Prenda312/Track-base-robot-CAD/motor/motor.SLDPRT

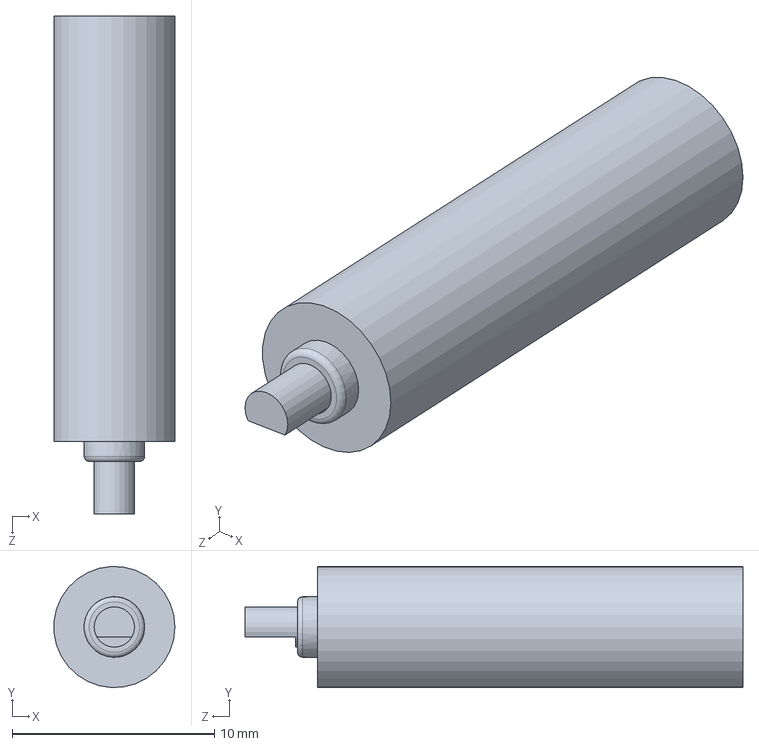
[picture p15: CAD file, 2024-11-09]
motor/motor.SLDPRT
5.98 x 5.99 x 24.6 mm
