Prenda312/Track-base-robot-CAD/worm/右旋蜗杆2×0.5-single.SLDPRT

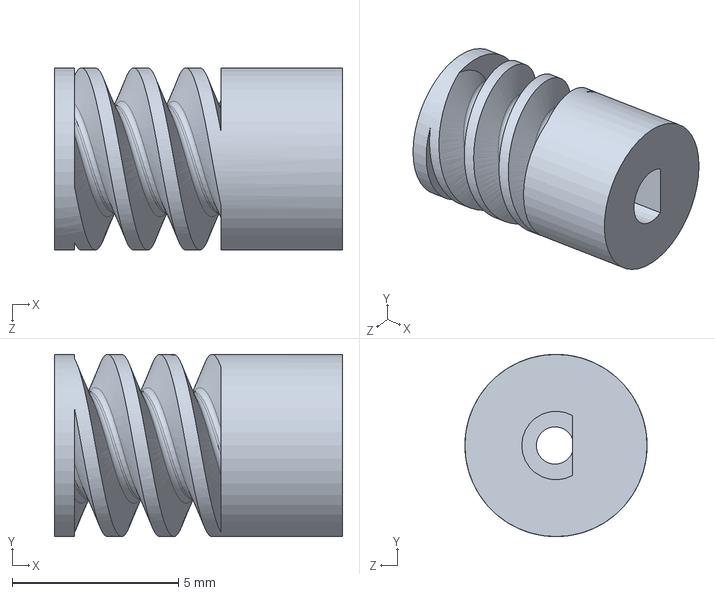
[picture p16: CAD file, 2024-11-09]
worm/右旋蜗杆2×0.5-single.SLDPRT
8.66 x 5.48 x 5.48 mm
