Prenda312/Track-base-robot-CAD/推力球轴承/推力球轴承_2.SLDPRT

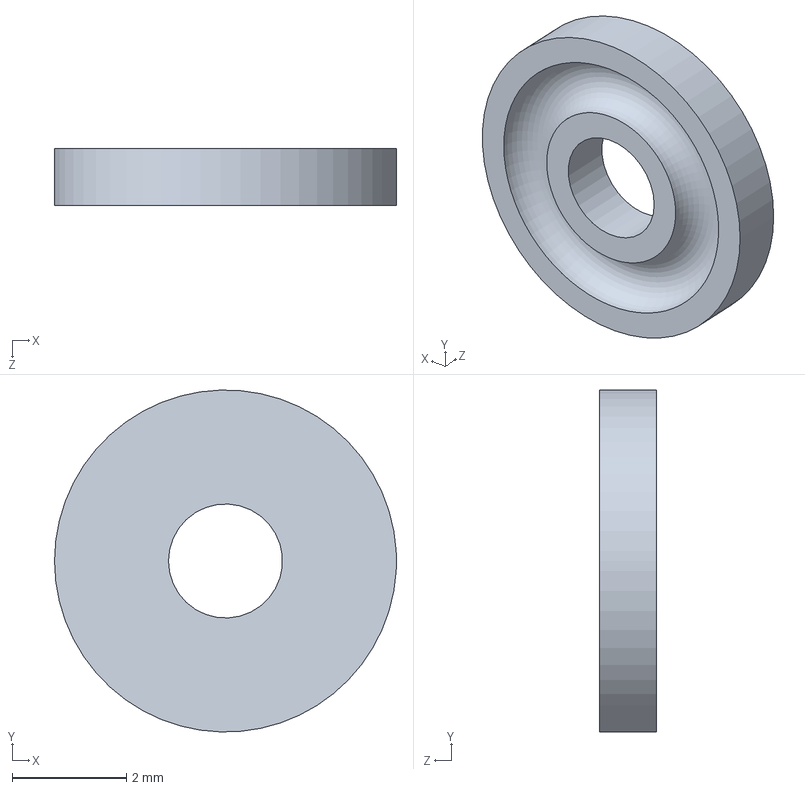
[picture p17: CAD file, 2024-11-09]
推力球轴承/推力球轴承_2.SLDPRT
6.00 x 6.00 x 1.00 mm
