Prenda312/Track-base-robot-CAD/轴/电机轴.SLDPRT

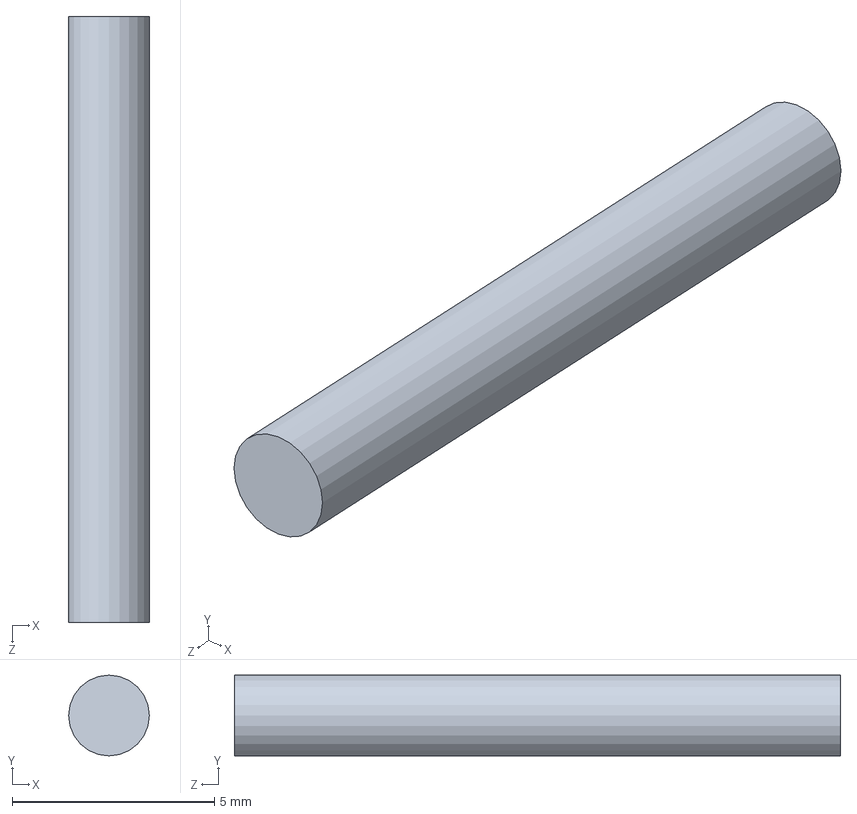
[picture p18: CAD file, 2024-11-09]
轴/电机轴.SLDPRT
2.00 x 2.00 x 15.0 mm
