Prenda312/Track-base-robot-CAD/motor/240-motor.SLDPRT

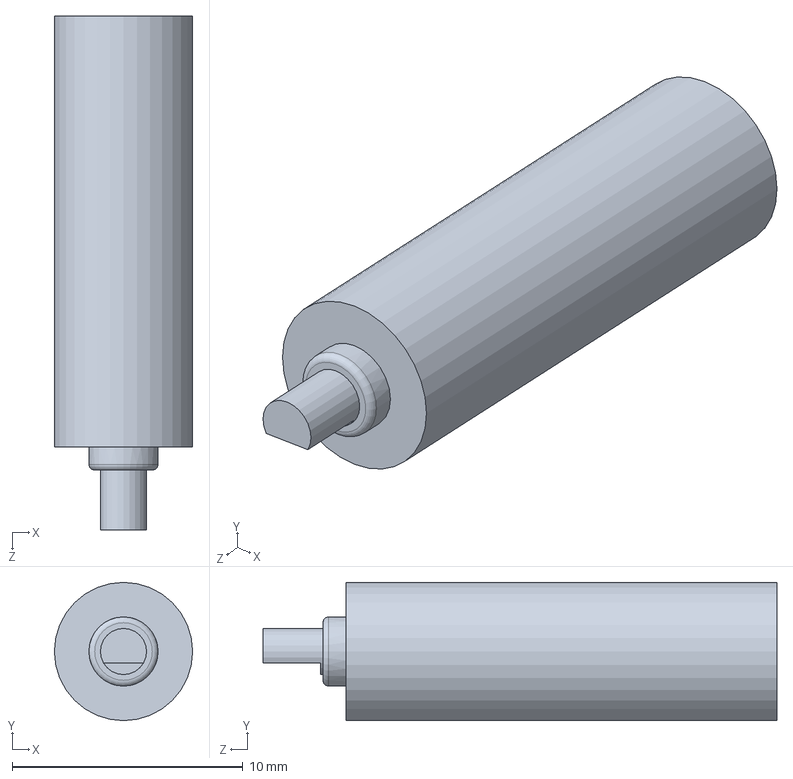
[picture p19: CAD file, 2024-11-09]
motor/240-motor.SLDPRT
6.00 x 6.00 x 22.3 mm
