Prenda312/Track-base-robot-CAD/spur gear-20×0.5.SLDPRT

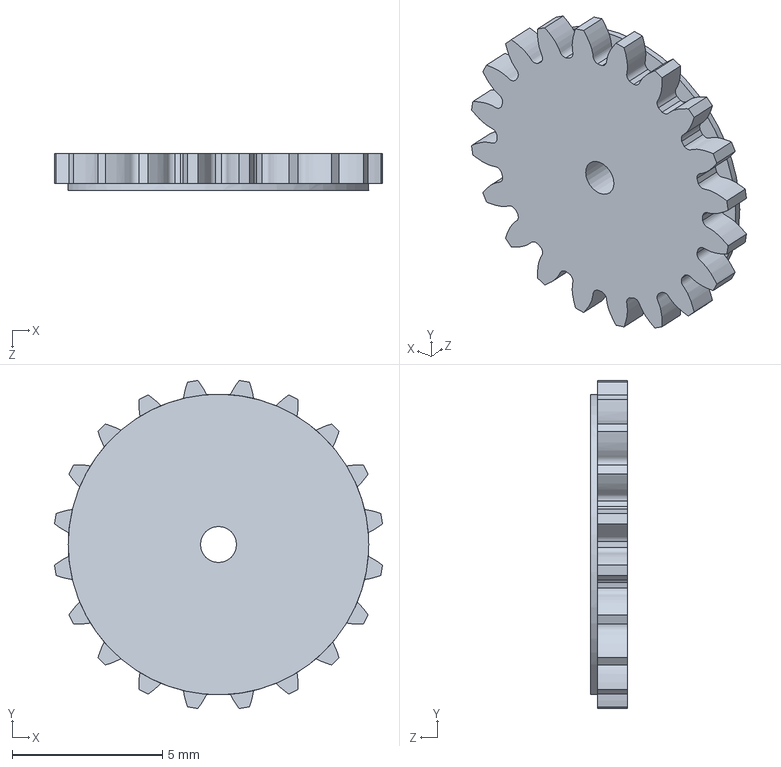
[picture p20: CAD file, 2024-11-09]
spur gear-20×0.5.SLDPRT
10.9 x 10.9 x 1.22 mm
