Prenda312/Track-base-robot-CAD/轴/8mm 轴.SLDPRT

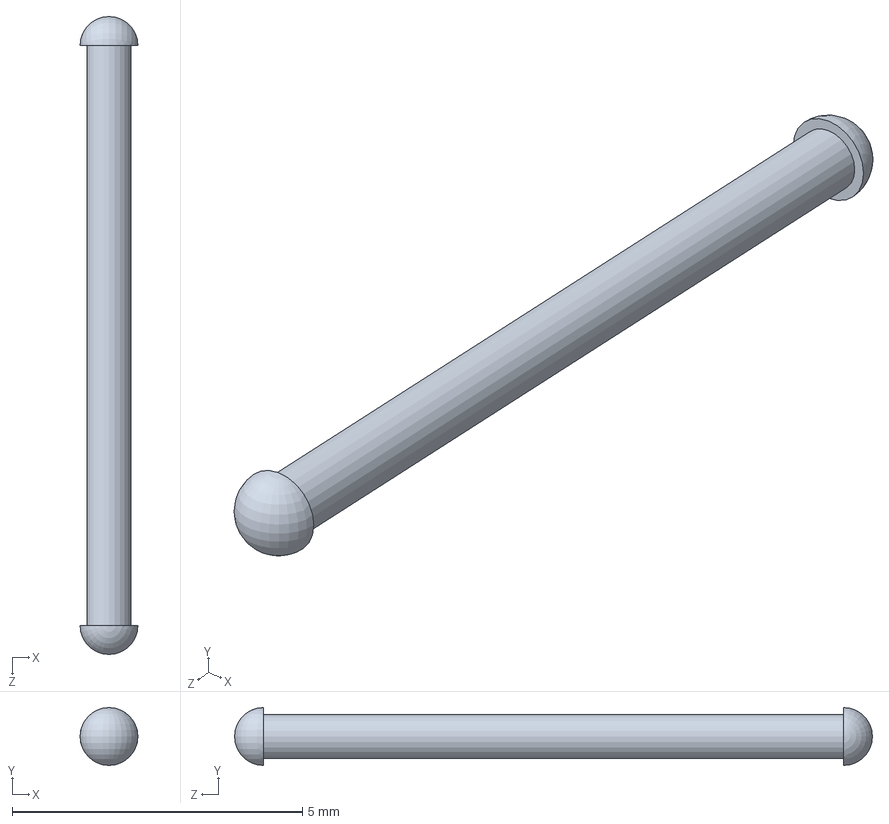
[picture p21: CAD file, 2024-11-09]
轴/8mm 轴.SLDPRT
1.00 x 1.00 x 11.0 mm
