Prenda312/Track-base-robot-CAD/camera.SLDPRT

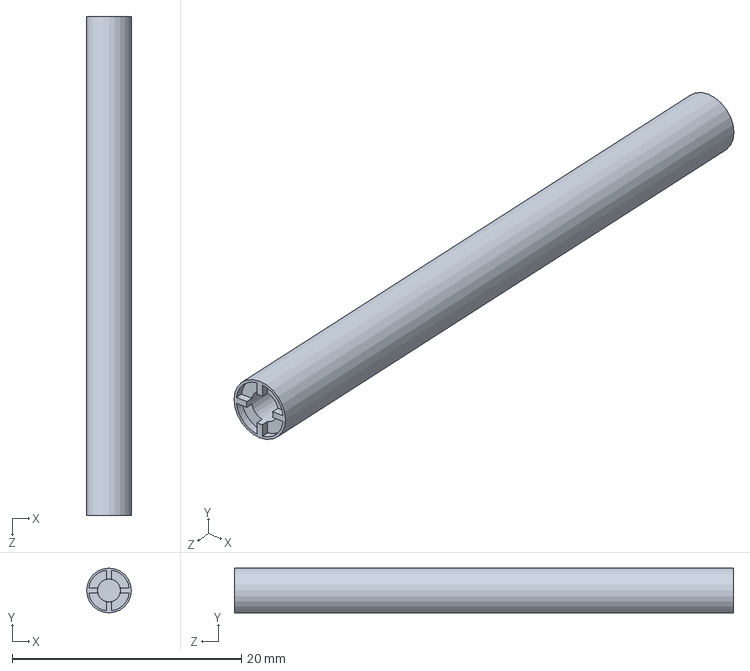
[picture p22: CAD file, 2024-11-09]
camera.SLDPRT
3.90 x 3.90 x 43.5 mm
