Prenda312/Track-base-robot-CAD/CMOS.SLDPRT

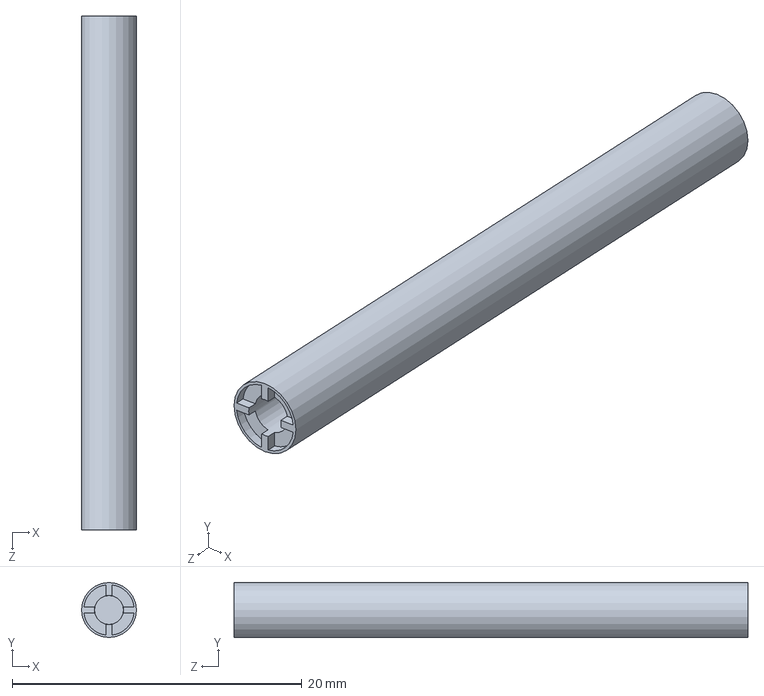
[picture p23: CAD file, 2024-11-09]
CMOS.SLDPRT
3.80 x 3.80 x 35.5 mm
