Prenda312/Track-base-robot-CAD/直齿锥齿轮14×1-100deg.SLDPRT

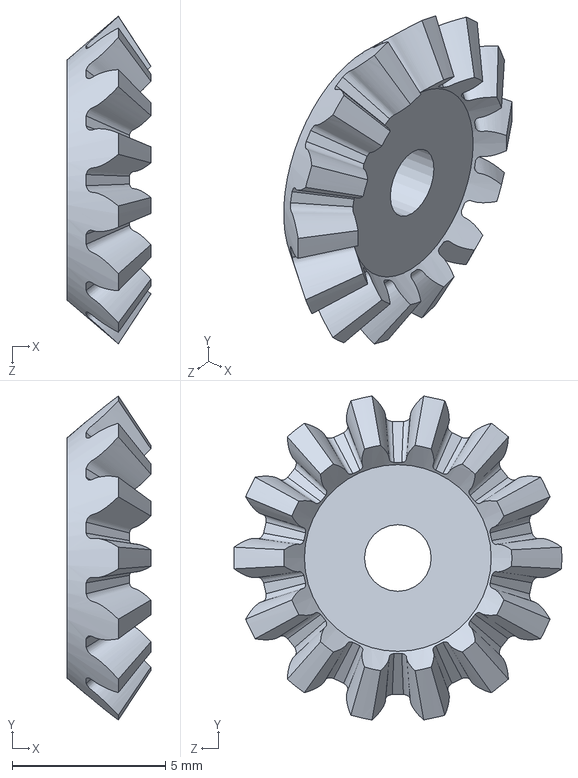
[picture p24: CAD file, 2024-11-09]
直齿锥齿轮14×1-100deg.SLDPRT
2.74 x 10.6 x 10.7 mm
