Prenda312/Track-base-robot-CAD/tread template final.sldprt

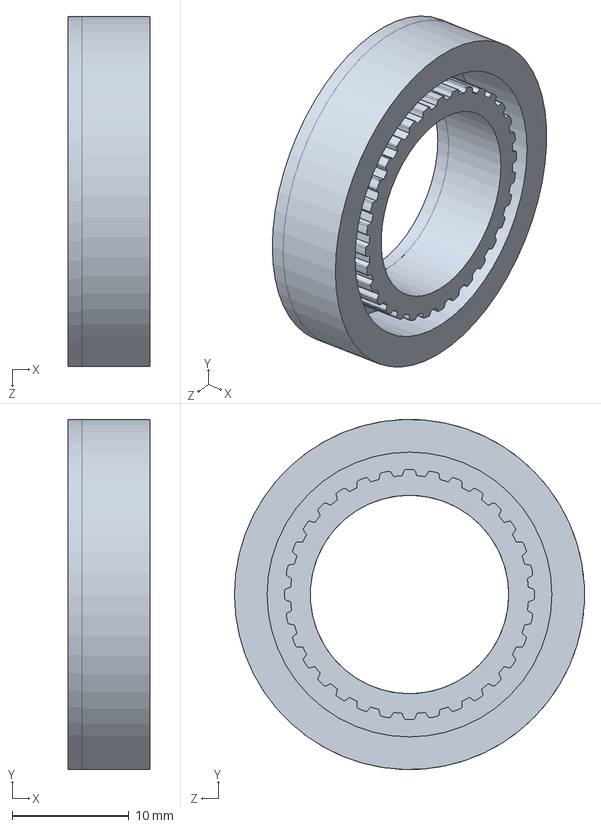
[picture p25: CAD file, 2024-11-09]
tread template final.sldprt
7.00 x 30.0 x 30.0 mm
