Prenda312/Track-base-robot-CAD/spur gear-10×0.5.SLDPRT

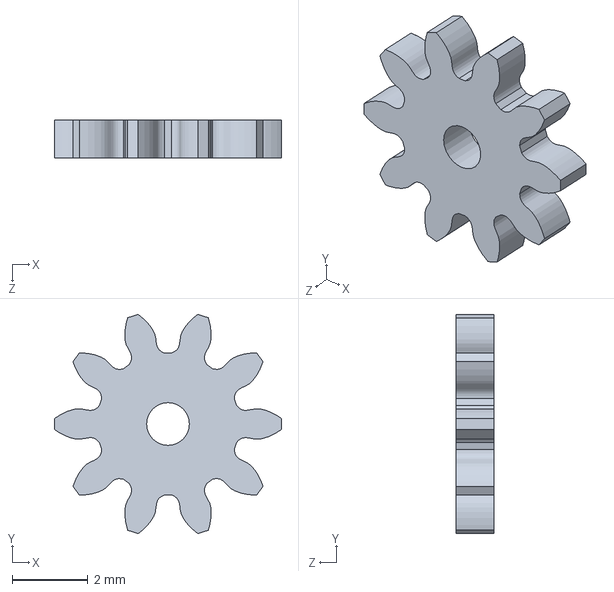
[picture p26: CAD file, 2024-11-09]
spur gear-10×0.5.SLDPRT
5.99 x 5.79 x 1.00 mm
