Prenda312/Track-base-robot-CAD/shell v3.SLDPRT

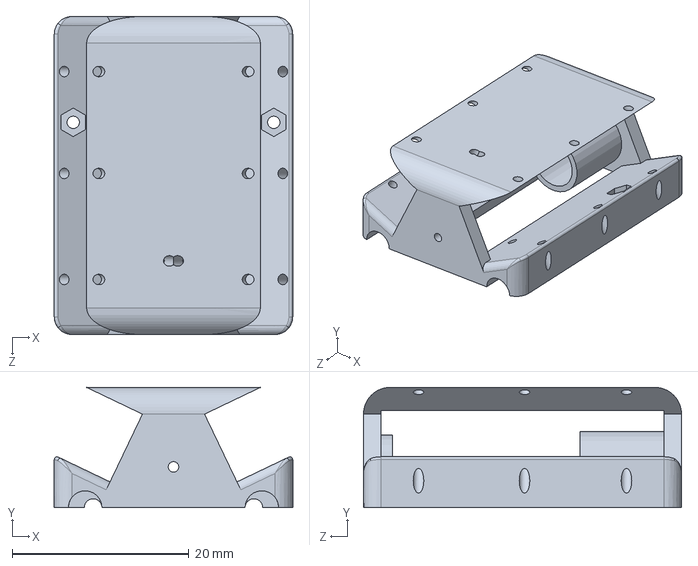
[picture p27: CAD file, 2024-11-09]
shell v3.SLDPRT
27.0 x 13.6 x 36.0 mm
