Prenda312/Track-base-robot-CAD/tread template part1 v2.STL

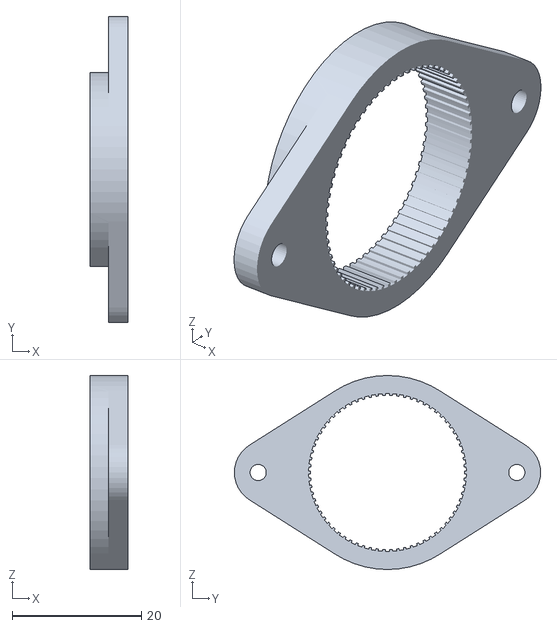
[picture p28: CAD file, 2024-11-09]
tread template part1 v2.STL
5.80 x 47.4 x 30.0
