Prenda312/Track-base-robot-CAD/tread template part2 v2.STL

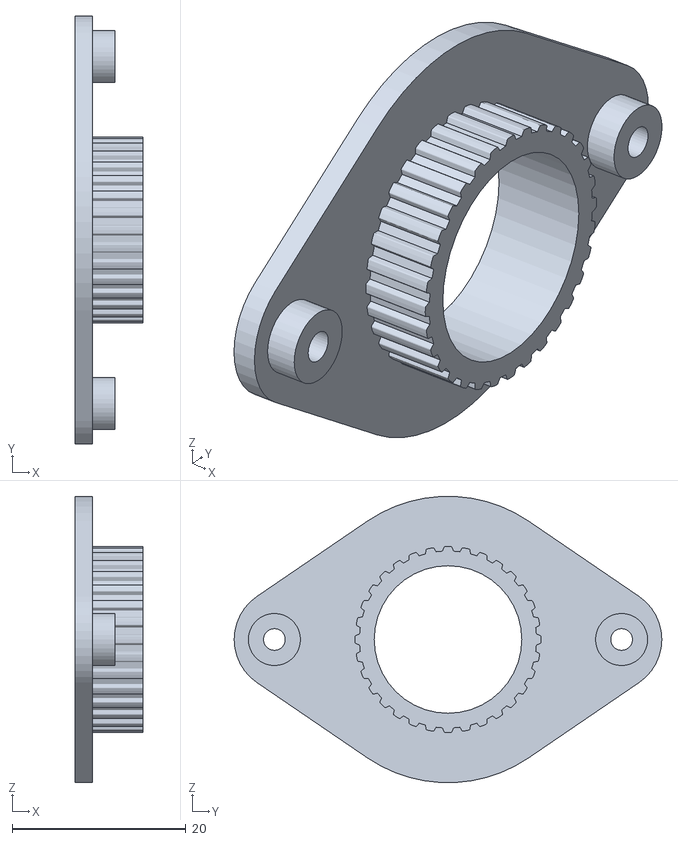
[picture p29: CAD file, 2024-11-09]
tread template part2 v2.STL
7.80 x 49.3 x 33.0
