Prenda312/Track-base-robot-CAD/spur mesh.SLDPRT

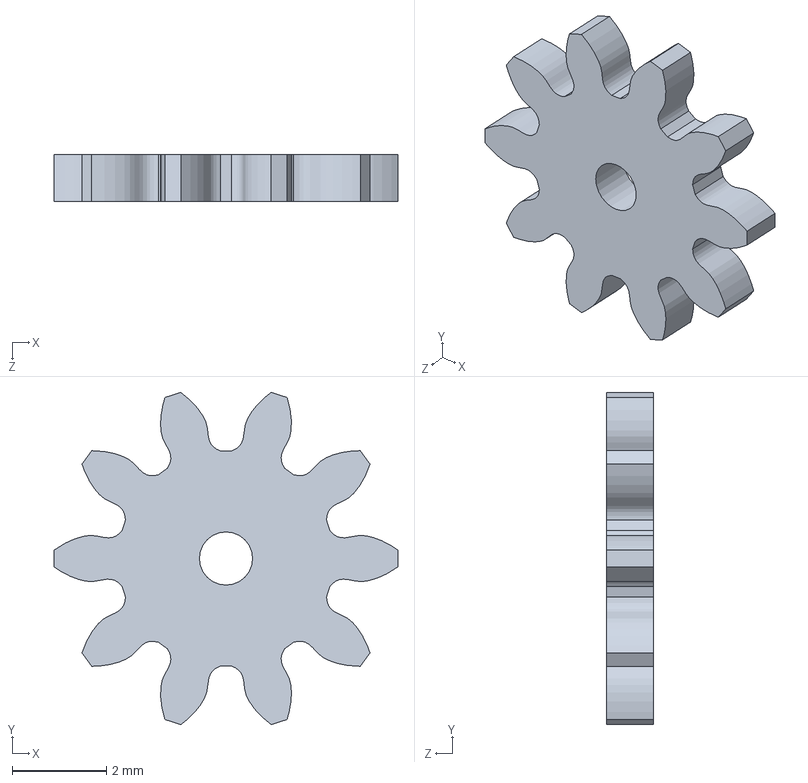
[picture p30: CAD file, 2024-11-09]
spur mesh.SLDPRT
7.30 x 7.06 x 1.00 mm
