Prenda312/Track-base-robot-CAD/tread template part1.STEP

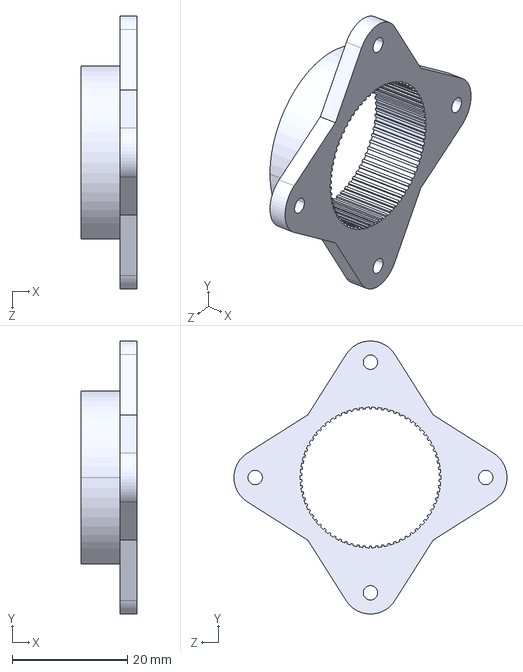
[picture p31: CAD file, 2024-11-09]
tread template part1.STEP
9.80 x 47.4 x 47.4 mm
