Prenda312/Track-base-robot-CAD/同步带.SLDPRT

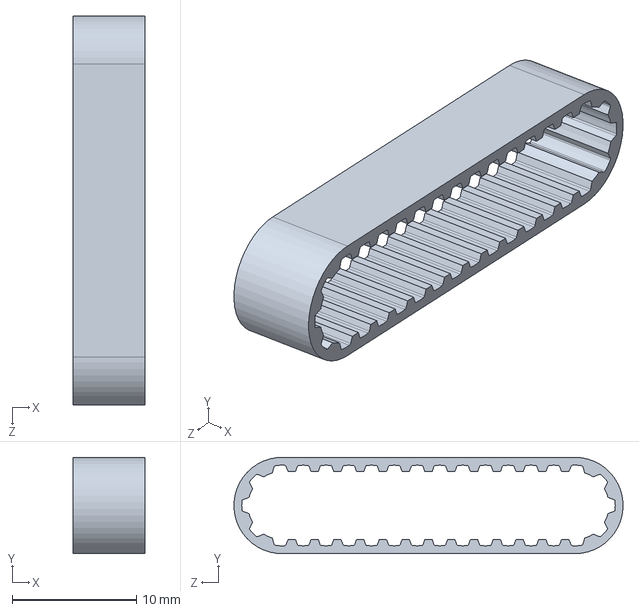
[picture p32: CAD file, 2024-11-09]
同步带.SLDPRT
5.80 x 7.74 x 31.3 mm
