Prenda312/Track-base-robot-CAD/弧齿锥齿轮14×1-100deg.SLDPRT

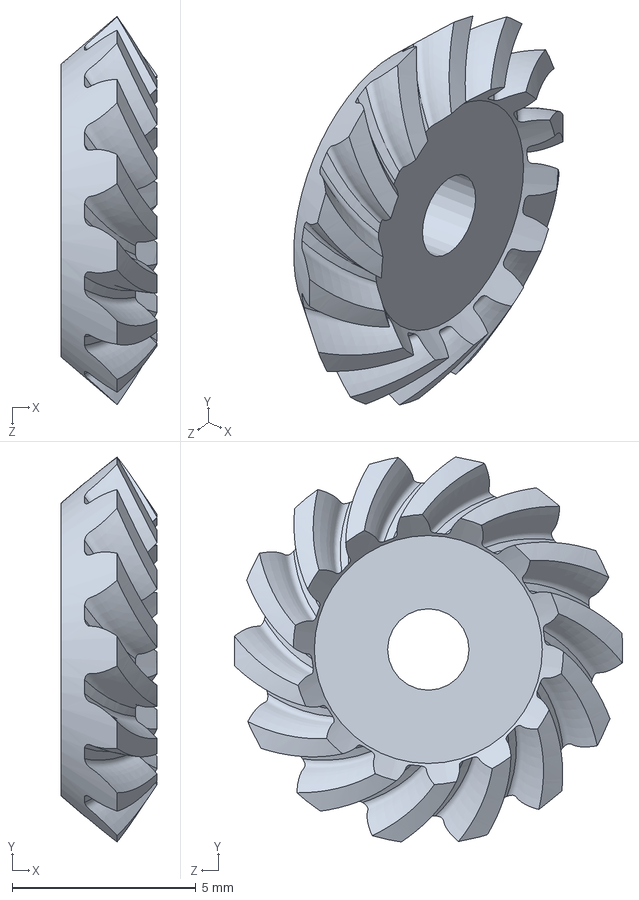
[picture p33: CAD file, 2024-11-09]
弧齿锥齿轮14×1-100deg.SLDPRT
2.62 x 10.5 x 10.6 mm
