Prenda312/Track-base-robot-CAD/pulley gear.SLDPRT

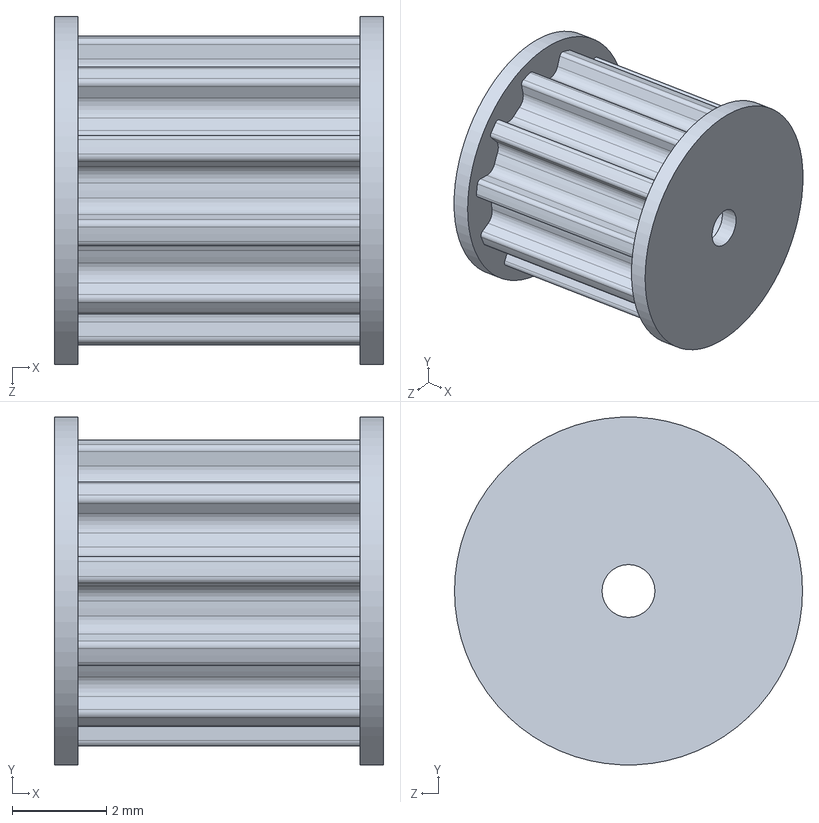
[picture p34: CAD file, 2024-11-09]
pulley gear.SLDPRT
7.00 x 7.39 x 7.40 mm
