Prenda312/Track-base-robot-CAD/spur gear-10×0.6.SLDPRT

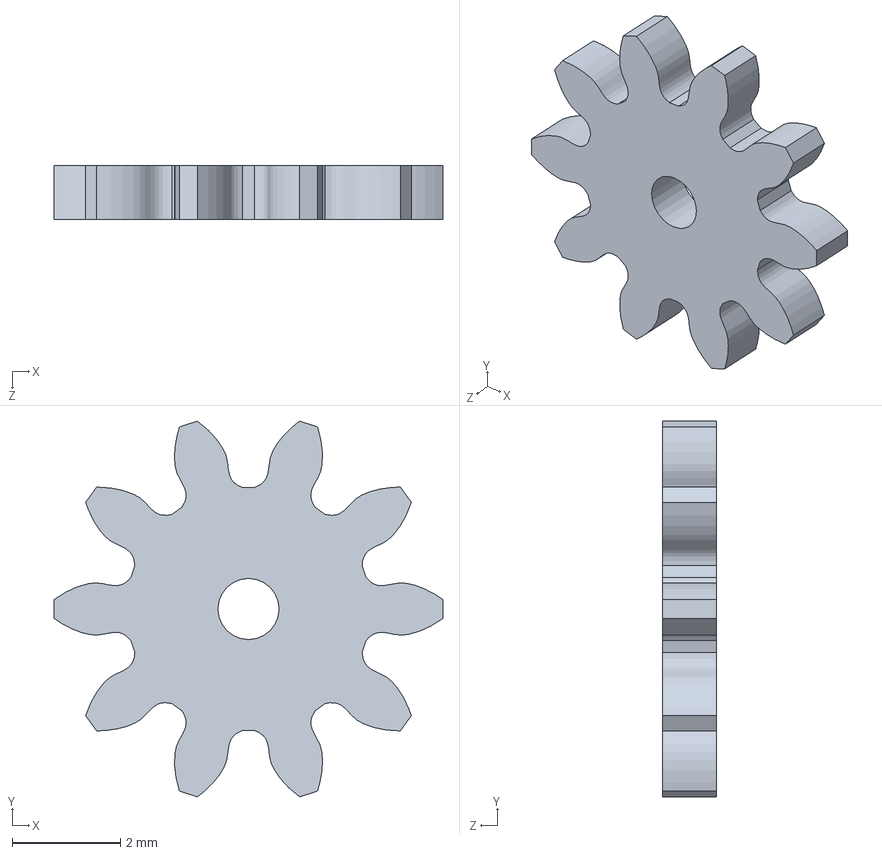
[picture p35: CAD file, 2024-11-09]
spur gear-10×0.6.SLDPRT
7.19 x 6.95 x 1.00 mm
