Prenda312/Track-base-robot-CAD/tread template.sldprt

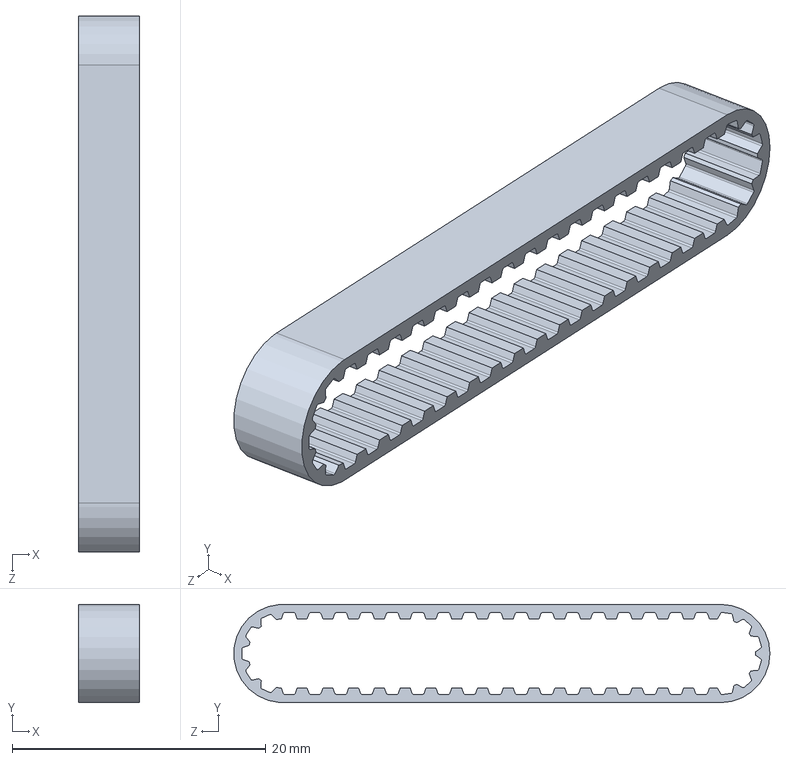
[picture p36: CAD file, 2024-11-09]
tread template.sldprt
4.80 x 7.74 x 42.3 mm
