Prenda312/Track-base-robot-CAD/spur.SLDPRT

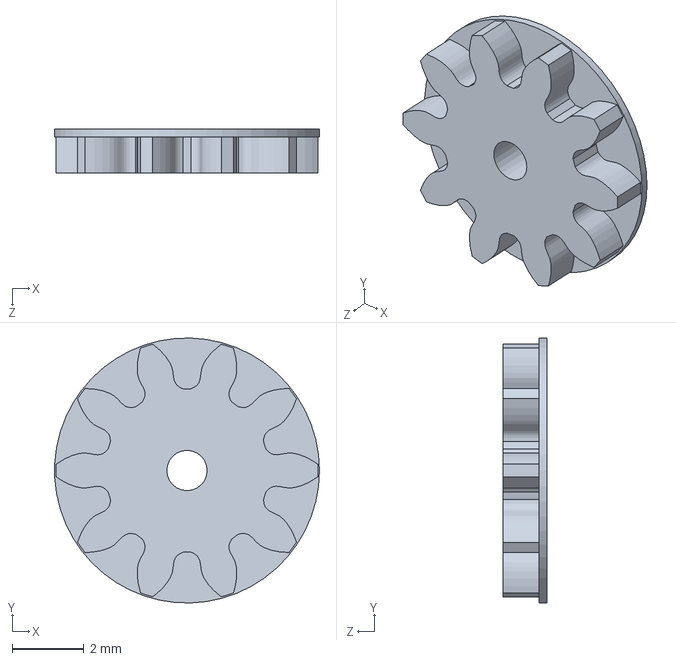
[picture p37: CAD file, 2024-11-09]
spur.SLDPRT
7.40 x 7.40 x 1.22 mm
