Prenda312/Track-base-robot-CAD/tread template part2.STEP

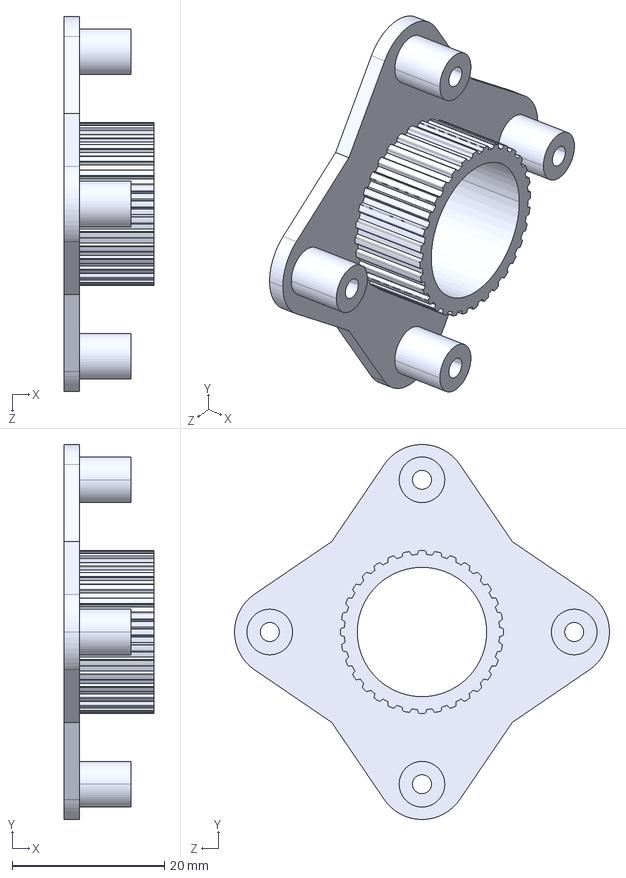
[picture p38: CAD file, 2024-11-09]
tread template part2.STEP
11.8 x 49.3 x 49.3 mm
