Prenda312/Track-base-robot-CAD/timing belt case.SLDPRT

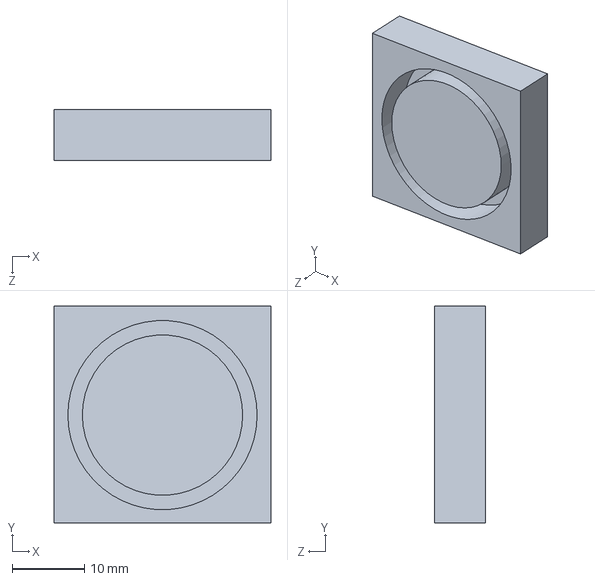
[picture p39: CAD file, 2024-11-09]
timing belt case.SLDPRT
30.0 x 30.0 x 7.00 mm
