Prenda312/Track-base-robot-CAD/tread template final v.sldprt

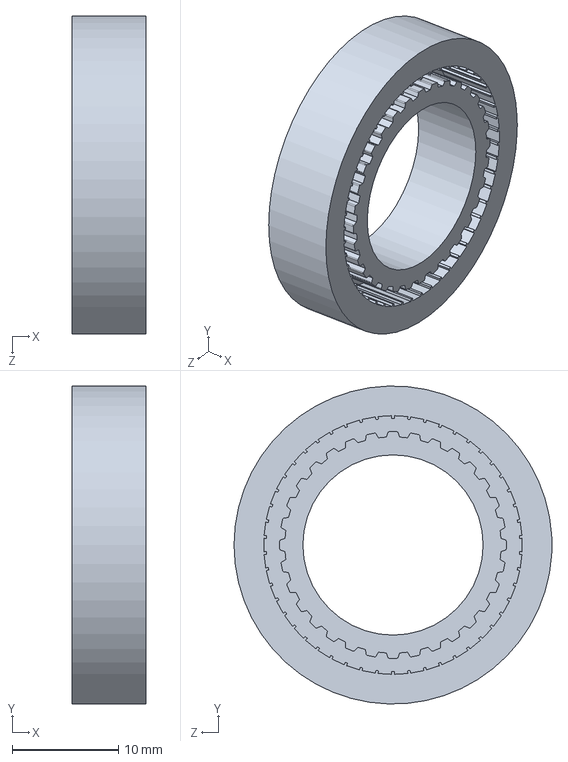
[picture p40: CAD file, 2024-11-09]
tread template final v.sldprt
7.00 x 30.0 x 30.0 mm
