Prenda312/Track-base-robot-CAD/Tread.SLDPRT

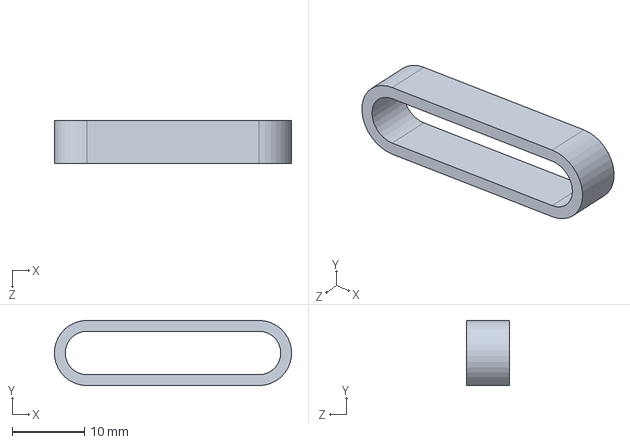
[picture p41: CAD file, 2024-11-09]
Tread.SLDPRT
32.7 x 9.00 x 6.00 mm
