Prenda312/Track-base-robot-CAD/同步带template.SLDPRT

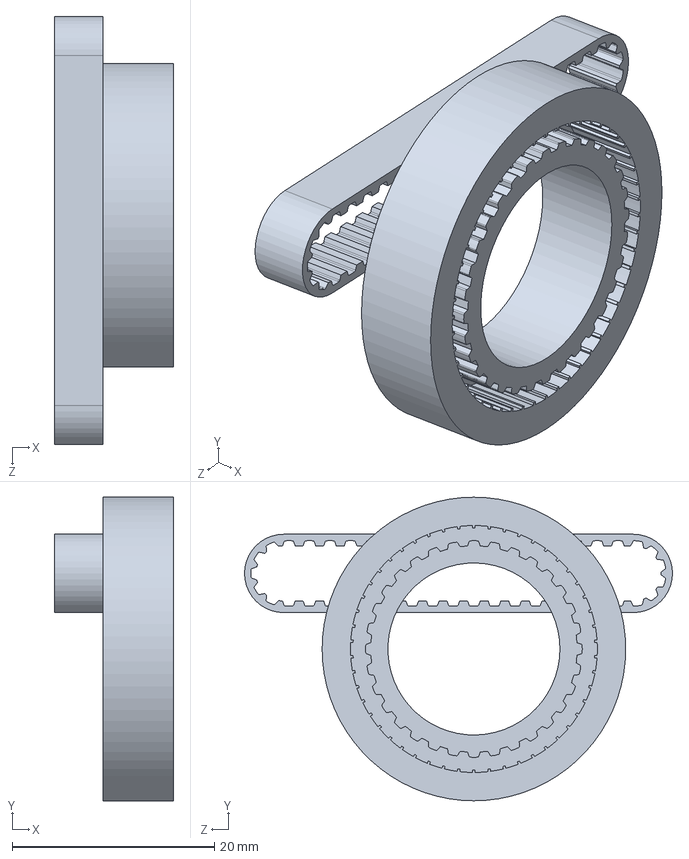
[picture p42: CAD file, 2024-11-09]
同步带template.SLDPRT
11.8 x 30.0 x 42.3 mm
