Prenda312/Track-base-robot-CAD/3mm bearing.SLDPRT

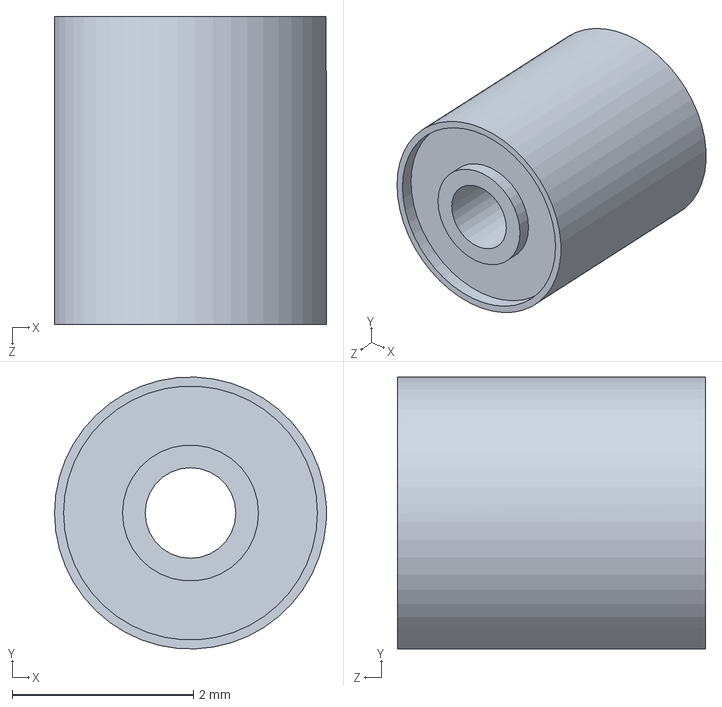
[picture p43: CAD file, 2024-11-09]
3mm bearing.SLDPRT
3.00 x 3.00 x 3.40 mm
