Prenda312/Track-base-robot-CAD/cam holder.SLDPRT

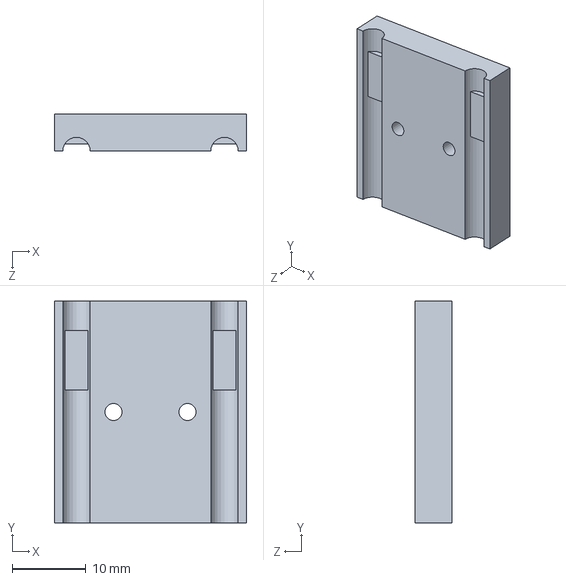
[picture p44: CAD file, 2024-11-09]
cam holder.SLDPRT
26.0 x 30.0 x 5.00 mm
