Prenda312/Track-base-robot-CAD/shell.SLDPRT

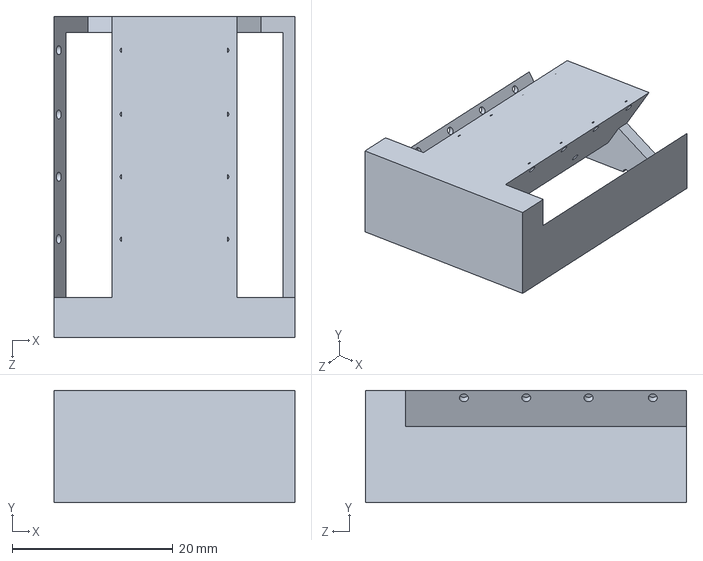
[picture p45: CAD file, 2024-11-09]
shell.SLDPRT
30.0 x 14.0 x 40.0 mm
