Prenda312/Track-base-robot-CAD/直齿锥齿轮14×1-100deg-motor.SLDPRT

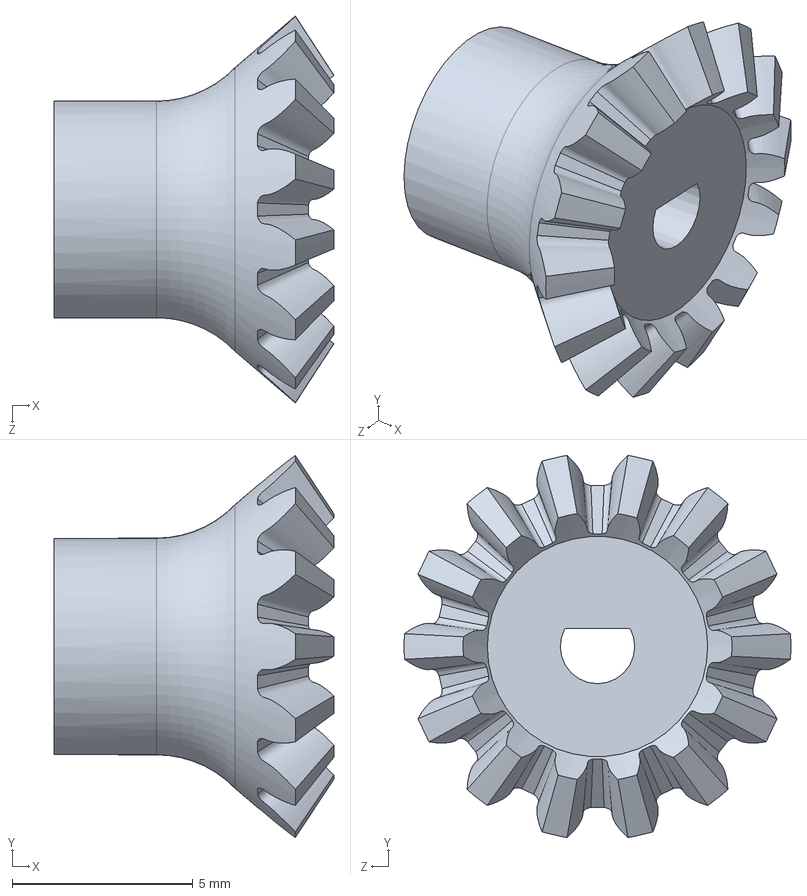
[picture p46: CAD file, 2024-11-09]
直齿锥齿轮14×1-100deg-motor.SLDPRT
7.74 x 10.6 x 10.7 mm
